GhlHub/open_ethernet_switch/ip_repo/INTERFACES.md

# Digital IP interface contracts

These contracts describe the checked-in RTL and KR260 production integration.
They do not extend port speed support. Manifests select source files, public
module names and catalog versions; changing the public hardware interface
requires a new catalog version and regeneration of dependent block designs.
The processor ABI is versioned separately by the capability register.

## Common packet and reset rules

Every switch-facing packet interface is 16-bit AXI-Stream with two byte
enables. A transfer occurs only with TVALID and TREADY high. The producer
holds data, byte enables, TLAST and any TUSER stable while stalled. TLAST
marks the final word; odd-length frames use one valid byte there. Byte lane
zero carries the earlier byte. Frames exclude the Ethernet preamble and FCS
at this boundary. Receive interfaces with TUSER convey frame error status.
An AXI-Stream slave is an input to the IP, not necessarily network ingress:
a port's slave stream transmits toward its PHY; the fabric's slave streams
receive from those ports.

Reset signals are active low. Integrators must provide domain-appropriate
reset release and stable clocks. Coordinated reset discards in-flight
packets, buffer ownership, learned addresses and hardware counter intervals.
Link-down/flush controls are the normal operational mechanism for removing
a port; arbitrary independent reset of a live producer/consumer is not an
advertised lossless recovery mechanism. The MAC additionally reclocks its
reset release internally. Existing CDC reports still require review; these
contracts are not physical CDC sign-off.

## Package boundaries

| Catalog name | Version / public module | Clocks and reset inputs | Interfaces / ownership |
| --- | --- | --- | --- |
| `gem_port` | 2.0 / `switch_gem_port` | `clk/rst_n`; `gem_rx_clk/gem_rx_rst_n`; `gem_tx_clk/gem_tx_rst_n` | 16-bit packet streams, PS GEM external RX-write/TX-read FIFO signals, two local counter banks |
| `pl_port` | 1.2 / `pl_gmii_mac_top` | `clk/rst_n`; `axis_clk/axis_rst_n`; `gtx_clk`, `clk_en` | Packet streams; 32-bit AXI-Lite MAC registers; 8-bit GMII; local counter bank |
| `sfp_port` | 1.1 / `sfp_port_top` | `clk/rst_n`; `axis_clk/axis_rst_n`; `gtx_clk/gtx_rst_n`; `gth_clk/gth_rst_n` | Packet streams; 32-bit AXI-Lite MAC registers; decoded 16-bit GTH data/control; PCS status; local counter bank |
| `switch_fabric` | 2.1 / `switch_fabric` | `clk/rst_n`; `axis_clk/axis_rst_n` | Five physical packet-stream pairs, CPU stream pair, four DDR AXI masters, shared packet buffers/queues, forwarding table, six counter banks |
| `management` | 2.1 / `switch_management` | `clk/rst_n` (production control clock) | 32-bit AXI-Lite controls, link/forward/learn masks, CPU TX ABI identifier and RX tag, statistics mailbox and 13-bank decoder |

In production, the fabric runs at 125 MHz, control at approximately
142.857 MHz, PL GMII at 125 MHz, and SFP PCS/GTH at 125/62.5 MHz. Packet
streams on all packages use `clk`; MAC AXI-Lite uses `axis_clk`.
The GEM FIFO clocks follow the negotiated link. The bridge is tested at
125/25/2.5 MHz, but KR260 GEM0 is restricted to 1 Gb/s by the current board
integration. GEM1 and both PL copper ports support full-duplex 10/100/1000 Mb/s.
SFP currently supports only 1 Gb/s full duplex. Faster SFP settings stored in
configuration are not implemented hardware capabilities.

PL RGMII, receive rate conversion, physical PHY reset and clock generation
remain board-shell dependencies. MDIO is a separate catalog IP. SFP GTH, clock generation and module sideband
protection also remain board-shell dependencies. Their eventual packaging
must preserve delay groups, reference clocks, reset ordering and pin timing.

## Fabric controls and DDR

Port numbering is GEM0=0, GEM1=1, PL0=2, PL1=3, SFP=4, CPU=5.
Physical ingress is `s00_axis` through `s04_axis`; physical egress is
`m00_axis` through `m04_axis`. `cpu_s_axis` receives CPU-originated frames;
`cpu_m_axis` delivers CPU-destined frames.

`m_axi_ing` writes physical ingress packets; `m_axi_egr` reads packets for
physical egress; `m_axi_cpu` reads/writes CPU packet transfers. Data width is
128 bits and address width 32 bits. Integration must preserve AXI handshakes,
burst responses and the DDR address mapping. The production interconnect
ties omitted cache attributes to zero explicitly. CPU AXI DMA descriptors
are owned by the R5/PS DMA path, not these fabric masters. See
[the memory map](../docs/memory-map.md) for allocation and ownership.

`link_up_i`, `link_flush_tog_i`, `fwd_en_i` and `learn_en_i` are provided
in the control domain; the fabric owns their crossings. Link/forward/learn
disable triggers the existing drain/invalidation behavior. CPU TX carries
[per-frame metadata](../docs/cpu-tx-metadata.md) in a mandatory two-byte stream
header; it has no separate override CDC. CPU RX tags are consumed in the
control domain once per retired RX descriptor.

Parameters `STATS_DDR` and `STATS_DEBUG` each accept 0 or 1 and must match
management and firmware. `AGE_TICK_DIVIDE_COUNT` controls the fabric aging
tick (default 25,000,000 cycles); it is shortened only in simulation fixtures.
The SFP's three `AN_*_CYCLES` timers default to short simulation values;
production explicitly sets all three to 1,250,000. Integrators must not
use the simulation defaults for a board image.

## Statistics mailbox

Management owns independent request selection and result storage for each
bank. Each bank has its own four-bit select, level request/acknowledgment,
stable 32-bit value and four-bit registered Gray activity signal. Source
logic owns clear-on-capture. Its handshake is request high, acknowledgment
high, request low, acknowledgment low. A timed-out processor access leaves
that bank's transaction intact while other banks progress. Software accumulates
intervals in memory; web/SNMP clients read those totals and per-bank freshness.

| Global banks | Management pins | Owner |
| --- | --- | --- |
| 0–1 | `gem0_req/acks/values` | GEM0 RX/TX |
| 2–3 | `gem1_req/acks/values` | GEM1 RX/TX |
| 4 | `pl0_req/acks/values` | PL0 |
| 5 | `pl1_req/acks/values` | PL1 |
| 6 | `sfp_req/acks/values` | SFP |
| 7–12 | `fabric_req/acks/values` | CPU, DDR and debug counters |

Flattened value vectors store the lowest bank in the least-significant
32-bit word. Banks 13–15 acknowledge immediately with zero; unimplemented
slots and disabled counter groups return zero. `STATS_TIMEOUT` defaults to
4095 control cycles. Timeout returns `0xFFFFFFFF` without canceling the
request or permitting a new index. Retry the same read and complete release
before selecting another index. See [statistics](../docs/statistics.md).

## Production address ownership

| Base / aperture | Owner |
| --- | --- |
| `0x80000000` / 64 KiB | PS-to-fabric AXI DMA |
| `0x80010000`, `0x80020000` / 64 KiB each | Board PL0/PL1 MDIO |
| `0x80030000` / 64 KiB | Board SFP I2C |
| `0x80040000`, `0x80080000` / 256 KiB each | PL0/PL1 MAC |
| `0x800C0000` / 256 KiB | SFP MAC |
| `0x80100000` / 64 KiB | Management, including indirect statistics |

Management 1.2 retires the CPU override at 0x4C and adds CPU_TX_ABI at 0x54.
Statistics capability bits, bank numbers and interrupt routing are unchanged.
`check_production_bd.py` checks these production addresses and connections.
Do not infer the deployed address map from the separate validation BD's
automatic address assignment.

## Fabric 1.2 MAC-table dump interfaces

`s_axi_dump` is an AXI-Lite slave clocked by fabric `clk` / `rst_n`.
Production maps it to control M08 at 0x80110000; SmartConnect supplies the
PS-control clock crossing. ABI register 0x00 reports 0x4D445001.

`m_axi_dump` is a write-only 128-bit AXI master on the same fabric clock/reset,
connected to HP0 SmartConnect S03. Its 16-beat, 256-byte INCR bursts have full
byte strobes and ID zero. One burst is outstanding at a time, with AxCACHE
tied to 0000 in production. Admission yields to address requests and
outstanding transactions from all four packet-DMA directions. An offered
AWVALID is retained under backpressure; later packet requests cannot retract
that burst.

MAC RAM port A grants dump reads below learning and aging, with preemption
between entries. Reads form 16-entry chunks; DDR waiting never holds the RAM
port. The 32 KiB destination belongs exclusively to DMA until completion,
including after a software timeout. The scan is live, not atomic.
See the [register, record and cache-ownership contract](../docs/mac-table-dump.md).

## PL PHY management (`pl_phy_mdio` 1.1)

One `switch_pl_phy_mdio` instance owns a separate MDIO bus, its IOBUF,
Clause 22 engine, AXI-Lite registers and DP83867 startup/polling sequencer.
`clk` and active-low `rst_n` use the 142.857 MHz control domain in the KR260.
`s_axi` has 32-bit data and 8-bit register addresses; the board reserves
64 KiB at `0x80010000` (PL0, PHY address 2) and `0x80020000` (PL1, address 3).
The existing register layout and divider defaults are preserved. Version 1.1
adds poll hold at offset `0x18` bit 0 and resolved status at `0x10` bit 10.
See [PL speed control](../docs/pl-ethernet-speeds.md) for ownership and sequencing.

`phy_reset_released_i` samples the board's clock-lock/PS-reset request through
two `ASYNC_REG` stages before starting initialization. It is a level, not a
pulse. The physical U19 reset request remains owned by the board shell.
`phy_link_o`, one-cycle `phy_link_change_o`, `init_done_o` and `init_fail_o`
are synchronous to `clk`. Link bits feed management inside the BD; change
pulses join SFP events in the board shell. `mdio_io` and `mdc_o` reach the
board pins directly. Package-pin/electrical constraints remain in board XDC;
this partition does not complete the outstanding external MDIO timing budget.

`INIT_PHY_ADDR`, `INIT_WAIT_CYCLES` and `INIT_POLL_CYCLES` are configurable.
Production retains the prior two-million-cycle startup wait and
1,430,000-cycle polling interval. Simulation models only the external IOBUF
primitive; the actual controller and sequencer come from the package.

PL MAC 1.1 adds `rx_byte_ce_i`, `tx_byte_ce_i`, and `port_mode_o[2:0]`.
Production sets `EXTERNAL_PACING=1`; the board RGMII shell owns rate conversion.
Legacy native GMII fixtures retain shared `clk_en` through the default parameter.
MAC register `0x41c` controls rate and physical enable; see the PL speed guide.

## Independent statistics mailboxes (ABI 2)

Management 2.0 owns one pending read/result per bank. Each endpoint now exports
four Gray clock-progress bits per bank. GEM 2.0 has independent RX/TX selects
(8 bits total); fabric 2.0 has six independent selects (24 bits). Management
exports separate `<endpoint>_select` buses and accepts corresponding
`<endpoint>_activity` buses. PL 1.2 and SFP 1.1 retain their four-bit select and
add four activity bits. Repackage all changed IP together; these interfaces
are not compatible with the former shared select. Source slots remain stable
through ACK release. A timed-out CPU access does not cancel source ownership.
See [statistics](../docs/statistics.md) for the CSR ABI and clock-progress CDC
contract. The serialized native fixture models successful transaction consumption
on request release; the production CSR uses an explicit take pulse, preserving
results across timeouts.

### STP/RSTP prerequisites (fabric and management 2.1)

No external port widths change. Fabric gates ordinary enqueue destinations by
forwarding state, while explicit directed CPU packets bypass it. CPU dequeue
requests pause at ingress-tag FIFO full. Management adds `STP_ABI` +0x58,
`0x53545002`, for firmware compatibility checking. See [protocol integration](../docs/spanning-tree.md).

## 10G SFP MAC/PCS (`sfp_10g_port` 1.0)

Selected by `KR260_SFP_MODE=10g`; the existing `sfp_port` stays the default.
The 10G core exposes 128-bit packet streams with 16 byte enables in the
125 MHz fabric domain, a compatible RX/TX-enable AXI-Lite window in the
management domain, and independent 64-bit/2-bit data/header interfaces in
the 156.25 MHz TX and recovered RX domains. Legacy `charisk` port names carry
sync headers; they are not 8b/10b controls. `rx_bitslip_o` and
`rx_reset_req_o` drive the external GTH shell. See the full
[clock, register, statistics and qualification contract](../docs/sfp-10g.md).

`switch_fabric` adds `SFP_DATA_WIDTH` (16 by default; select 128 with this IP).
Only `s04_axis` and `m04_axis` widths change; other packet ports and the DDR
ABI remain unchanged. Standalone consumers must apply the included upstream
FIFO timing constraints and constrain all status/control CDC paths; merely
packaging the core does not establish timing closure.

## Dual-rate SFP

`sfp_dual_port` preserves the 128-bit stream and AXI-Lite management interfaces
of `sfp_10g_port`. Additional 125/62.5 MHz clocks serve the 1G PCS. Stable mode
request plus a retry toggle cross to the always-on GTH controller; active mode,
ready and error return through synchronizers. See [the complete contract](../docs/sfp-dual.md).
