GhlHub/open_ethernet_switch/docs/ip-partitioning.md

# IP repository partitioning

## Implemented boundaries

The first structural migration separates forwarding/storage from all five
physical port endpoints. No packet pipeline stage, FIFO depth, clock,
reset sequence, register address, counter index or firmware ABI is changed.

```mermaid
flowchart LR
    PS[PS GEM external FIFOs] <--> GEM[gem_port x2<br/>CDC and port counters]
    RGMII[Board RGMII I/O<br/>elastic buffers] <--> PL[pl_port x2<br/>GMII MAC and counters]
    PHY[PL copper PHYs] <--> MDIO[pl_phy_mdio x2<br/>MDIO, initialization and polling]
    MDIO -. link status .-> MGMT
    GT[Board GTH and clocks<br/>SFP sideband] <--> SFP[sfp_port<br/>1000BASE-X MAC and PCS]
    GEM <-->|16-bit AXI-S| FAB
    PL <-->|16-bit AXI-S| FAB
    SFP <-->|16-bit AXI-S| FAB
    subgraph FAB[switch_fabric]
        IN[Physical ingress datapath]
        BUF[Shared buffer manager]
        OUT[Physical egress datapath]
        CPU[CPU virtual-port engines]
        FWD[MAC lookup, learning and aging]
        IN <--> BUF
        OUT <--> BUF
        CPU <--> BUF
        FWD -. destination masks .-> IN
        FWD -. destination masks .-> CPU
    end
    FAB <-->|Four AXI masters| DDR[Board interconnect and PS DDR]
    CPU <-->|16-bit AXI-S| DMA[AMD AXI DMA and R5]
    MGMT[management<br/>AXI-Lite configuration and snapshot mailbox] -. control and status .-> FAB
    GEM -. snapshots .-> MGMT
    PL -. snapshots .-> MGMT
    SFP -. snapshots .-> MGMT
```

`ip_repo/switch_fabric/hdl/switch_fabric.sv` owns the shared buffer manager,
physical ingress/egress, CPU virtual port and forwarding table. The buffer
manager is a sibling of `ingress_datapath`, rather than a child of ingress.
`rtl/dma/ingress_top.sv` remains a compatibility assembly for existing
ingress subsystem tests and instantiates the same ingress datapath.

`ip_repo/gem_port/hdl/switch_gem_port.sv` combines the existing GEM bridge
with its RX and TX counter banks. `rtl/switch_top.sv` is now a wiring
assembly of the fabric and five endpoints, plus the unchanged statistics
bank decoder. It preserves the existing testbench port list. The production board now
uses `ip_repo/production.tcl` to instantiate the catalog cells directly
in `system.bd`; `kr260_pl_top` contains only the physical shells, clocks,
reset synchronizers and physical status/event logic. The two `pl_phy_mdio`
catalog instances now own MDIO, initialization, polling and PHY reset-release
synchronization.

The other three IP manifests package the existing PL MAC, SFP MAC/PCS and
management modules. `scripts/ip_sources.py` deduplicates shared leaf RTL
and orders packages before modules. Simulation, out-of-context switch
synthesis and the board build use this resolver, replacing the board's
recursive source glob. `build/switch_top_files.f` is a compatibility list;
the manifests are authoritative.

## Interface contracts

| Boundary | Contract |
| --- | --- |
| Physical fabric ingress | `s00_axis` through `s04_axis`; 16-bit data, two byte enables, valid/ready/last, bad-frame `TUSER`; fabric clock |
| Physical fabric egress | `m00_axis` through `m04_axis`; 16-bit data, two byte enables, valid/ready/last; fabric clock |
| CPU streams | Existing 16-bit `cpu_s_axis`/`cpu_m_axis`, fabric clock |
| DDR | Existing 32-bit addresses, 128-bit data, physical write master, physical read master, bidirectional CPU master |
| Port numbering | GEM0=0, GEM1=1, PL0=2, PL1=3, SFP=4, CPU=5 |
| Statistics | Existing four-phase request/ack handshake; select remains stable through completion; held snapshot data and clear-on-read behavior unchanged |
| Counter ownership | GEM banks 0–3 inside GEM endpoints; PL/SFP banks 4–6 inside MAC endpoints; CPU/DDR/debug banks 7–12 inside fabric |
| Resets and CDC | Physical endpoint CDC remains local; fabric runs at 100 MHz; management and MAC control use the existing PS control clock |
| Parameters | Fabric exposes only `STATS_DDR`, `STATS_DEBUG`, and `AGE_TICK_DIVIDE_COUNT`; imported package geometry is not a GUI parameter |

The adapters retain their existing frame/FCS conventions and backpressure
rules. This migration does not add PL 10/100 operation or faster SFP rates.
The CPU override and RX-tag paths retain the baseline behavior, including
the previously documented unresolved concurrency/CDC concerns.

## Verification

The reference is Git commit `6b180e0138d5592cfb80078a9a2517d63013927b`.
`scripts/check_ip_equivalence.py` retrieves its original switch and ingress
assemblies and compares them with the partitioned design under identical
inputs and DDR responses. Every external output is compared after every
relevant clock edge, including statistics data/acknowledgments. It also
runs the existing packet-content and control regression assertions.

All four combinations of `STATS_DDR` and `STATS_DEBUG` passed:

| DDR/debug | Clock samples | Outputs per sample | Completed snapshot reads |
| --- | ---: | ---: | ---: |
| 0/0 | 29,922 | 114 | 1,591 |
| 1/0 | 29,922 | 114 | 1,366 |
| 0/1 | 29,922 | 114 | 1,543 |
| 1/1 | 29,922 | 114 | 1,326 |

The stimulus covers GEM0-to-CPU forwarding, byte contents, link flushing,
blocked data traffic, reserved control-frame delivery, CPU destination
override and return to normal forwarding. Snapshot traffic spans all bank
and slot values, including unmapped banks. This is a finite simulation
comparison, not formal equivalence or an all-port stress proof.

The module regression passed buffer-manager, ingress, egress, GEM bridge,
egress/GEM integration, PL adapters, SFP port, CPU port, forwarding,
statistics, multirate GEM, ingress pipeline and diagnostics tests.

Packaging checks compare staged source contents with the manifests and
assert interface widths, unique clock associations, resets and the legal
fabric parameter list. Generated IP wrappers are additionally exercised
through the same comparison fixture; Vivado integrity checking alone did
not detect its initial erroneous promotion of package constants into
module parameters. The packaging script explicitly corrects this.

Local evidence is under `build/ip_refactor/`. The isolated board project
is `build/vivado_kr260_modular/`; its implementation result is recorded in
[verification](verification.md).

## Production block design

`system.bd` contains `fabric`, `gem0`, `gem1`, `pl0`, `pl1`, `sfp` and
`management` catalog cells alongside PS, DMA and SmartConnect. All ten
physical AXI-Stream connections, CPU streams, three DDR masters, MAC control
interfaces, GEM external FIFOs, interrupts and management controls connect
inside the BD. The existing address windows remain:

| Block | Base | Window |
| --- | --- | --- |
| CPU AXI DMA | `0x80000000` | 64 KiB |
| PL0 / PL1 MDIO | `0x80010000` / `0x80020000` | 64 KiB each |
| SFP I2C | `0x80030000` | 64 KiB |
| PL0 / PL1 MAC | `0x80040000` / `0x80080000` | 256 KiB each |
| SFP MAC | `0x800C0000` | 256 KiB |
| Management | `0x80100000` | 64 KiB |

`STATS_DDR` and `STATS_DEBUG` now configure both fabric and management IP
parameters in the build Tcl. Physical instances stay under `u_pl`, preserving
the RGMII delay groups and forwarded-clock constraint targets.
The clock-crossing XDC is processed late, after vendor and board clocks
exist; its numeric bounds are unchanged.
`axi_attributes.tcl` explicitly retains the previous `AxCACHE=0000` ties
on all four switch DDR channels; Vivado otherwise defaults omitted cache
attributes to `0011`. There is no firmware ABI change. A missing or stale
catalog fails the build before BD creation; regenerate it into a fresh
directory and set `KR260_IP_CATALOG`.

To compare the generated production datapath with the original assembly:

```sh
python3 scripts/check_ip_equivalence.py \
  --production-bd build/ip_refactor/production_bd/project/kr260_switch.gen/sources_1/bd/system \
  --catalog build/ip_catalog
```

This fixture uses the generated instance connections and packaged source
snapshots, checks the stream/control wiring against the prior native
assembly, and reuses the packet/counter equivalence stimulus. Only aging
and PCS timers are accelerated in fixture-local wrapper copies. PS/DDR
interconnect and physical I/O remain simulation boundaries. The all-counter
production assembly passed this comparison and completed bitstream generation
with routed WNS +0.018 ns and hold slack +0.011 ns; see
[build results and limitations](verification.md#2026-09-25-production-catalog-block-design).
It was downloaded over JTAG and passed settled GEM1/PL0 connectivity, SNMP
and HTTP checks; see the board acceptance results in verification.md.

## Independent package verification

Each digital IP now owns a test manifest. `make -C sim sim-ip-regression`
runs its focused tests from native and packaged RTL, then the existing
whole-switch comparisons for all four counter configurations. Public tops
are independently elaborated; GEM/PL/SFP and management have direct boundary
benches, while fabric behavior is checked through its constituent suites
and assembly miter. See [suite coverage and commands](../ip_repo/README.md#independent-ip-regression-suites).

## PL PHY-management extraction

`pl_phy_mdio` 1.0 moves both MDIO controllers and their two-stage PHY-reset
release synchronizers into the catalog. The production instances are `mdio0`
and `mdio1`; each owns initialization, polling and its bidirectional IOBUF.
The former 34 AXI-Lite signals between `system.bd` and `kr260_pl_top` are now
internal BD interfaces. The board retains PHY reset requests, RGMII I/O and
clock generation. PHY link status connects directly to management; change
pulses join existing SFP events in the physical shell.

No firmware registers, PHY addresses, polling intervals or startup delays
change. This split makes PHY management independently reusable before the
more constraint-sensitive RGMII migration. Its focused tests use actual
packaged RTL with a simulation-only IOBUF primitive. They cover Clause 22
read/write framing, status clear, startup at both board PHY addresses,
strap/ID failure, link polling, disconnect/reconnect, PHY reset and deferred
CPU requests during polling. Existing MDIO arbitration/AXI race investigations
remain listed in the inventory; packaging does not resolve those issues.

## Remaining migration and acceptance work

The reusable **digital** IP boundaries are implemented. The complete
physical-port/block-design migration proposed for the final architecture
is not complete:

1. Move each RGMII I/O/elastic-buffer shell inside its copper-port IP,
   composing it with the now-packaged `pl_phy_mdio` management block,
   with scoped constraints and explicit per-instance IDELAY groups. The
   current board constraints name `u_pl/u_rgmii0` and `u_pl/u_rgmii1`, so
   this requires a separate physical timing check.
2. Move the GTH, PCS clock generator and SFP sideband shell into the SFP
   package, with reproducible vendor-IP dependencies and scoped clocks.
3. Management 1.1 now includes the statistics decoder. The separate
   `partition_validation.bd` remains an interface test fixture; keep its
   clock/address defaults distinct from production.
4. Add a six-port concurrent packet scoreboard with randomized DDR
   backpressure/errors, exhaustion, link/reset transitions and ownership
   invariants. Existing subsystem tests and the finite comparison do not
   replace that coverage.
5. After routed timing/CDC review, repeat board DHCP, ping, forwarding,
   GEM1 speed, SNMP/web and SD configuration regression. Do not attribute
   existing STP or transient outage problems to this structural migration
   without new evidence.

The partitioned all-counter image has subsequently been loaded over JTAG.
DHCP, CPU connectivity, web/SNMP access and settled endpoint forwarding
passed on the connected GEM1/PL0 path. Initial DHCP/endpoint losses were
observed before recovery; see [hardware results](verification.md). The
remaining all-port and speed-matrix acceptance work still applies.

## Management 1.1 and reproducible acceptance

The statistics router is now inside `switch_management`; production no longer
uses a router module reference. Public per-bank signals replace the four raw
mailbox wires. Firmware ABI, register offsets and bank numbering are unchanged.
A public-wrapper test covers all 256 index values, clear-on-read isolation,
invalid banks, saturation, backpressure and stopped-clock timeout recovery.

[Interface contracts](../ip_repo/INTERFACES.md) describe the current packages.
`python3 scripts/verify_ip_flow.py` regenerates a catalog and production BD in
fresh output directories, then runs package and assembly regressions. Use
`--implement` to add PNR/bitstream generation and routed reports. The production
packet miter substitutes the CSR source with its existing mailbox stimulus;
the separate management-wrapper test verifies AXI-Lite-to-bank behavior.

## Fabric 1.2: MAC-table dump master

The dump engine belongs inside `switch_fabric`, alongside MAC port-A arbitration
and packet-DMA admission tracking. It exports `m_axi_dump` (128-bit writes, HP0
S03) and `s_axi_dump` (control M08, 0x80110000), both on the fabric clock.
Control SmartConnect now has nine outputs and HP0 SmartConnect four inputs.
Manifest-owned source/tests and native/production equivalence include both new
interfaces. Physical shells and the HP1 CPU stream DMA retain their interfaces.
See [the complete contract](mac-table-dump.md).
