GhlHub/open_ethernet_switch/docs/source-notices.md

# Source provenance and reference material

[`rtl/pl_gmii/open_eth_mac_1g_switch.sv`](../rtl/pl_gmii/open_eth_mac_1g_switch.sv)
identifies its origin as `open_eth_mac_1g` from
[GhlHub/open-ethernet-cores](https://github.com/GhlHub/open-ethernet-cores).
Its existing `GPL-3.0-or-later` SPDX identifier and modification notice (now four changes, the newest a descriptor-ring "full" width bug fix) are
preserved. The notice describes the module rename, permanently enabled
destination acceptance for switch operation, and two clock-domain-crossing changes
(the reset inputs are reclocked into each clock domain, and the data read
pointers are published one word per clock), with no change to the frame path. The original import does not
record an upstream commit ID.

[`rtl/mdio/open_eth_mdio_master.sv`](../rtl/mdio/open_eth_mdio_master.sv) is
identified by its header as imported from the same upstream project's
`open_eth_sgmii_pcs_pma` IP (a Clause 22 MDIO station-management master,
upstream only instantiated inside that larger core, used standalone here).
Its existing `GPL-3.0-or-later` SPDX identifier is preserved; the original
import does not record an upstream commit ID.
[`rtl/mdio/mdio_controller.sv`](../rtl/mdio/mdio_controller.sv) (and its sim
model) is new project code wrapping it with an AXI4-Lite register interface.

A copy of the GPL version 3 text is included at
[`LICENSES/GPL-3.0-or-later.txt`](../LICENSES/GPL-3.0-or-later.txt).
This inventory does not assign a new license to the other source files.

[`rtl/sfp_pcs/autoneg_1000base_x.sv`](../rtl/sfp_pcs/autoneg_1000base_x.sv)
records design cross-checks against
[freecores/1000base-x](https://github.com/freecores/1000base-x), specifically
`rtl/verilog/ge_1000baseX_tx.v` and `ge_1000baseX_an.v`. No reference commit is recorded. These are design references, not protocol
conformance evidence. The implementation's reductions and unverified areas are
listed in its header and the [development inventory](inventory.md).

The GEM adapters refer to the AMD
[Zynq UltraScale+ technical reference manual (UG1085)](https://docs.amd.com/r/en-US/ug1085-zynq-ultrascale-trm).
The local downloaded PDF is reference material and is not included in the
source commit. Board documentation is available in the
[KR260 user guide (UG1092)](https://docs.amd.com/r/en-US/ug1092-kr260-starter-kit).

The SFP transceiver wrapper depends on AMD Transceiver Wizard IP. Its
[`gth_sfp_ip.xci`](../rtl/sfp_pcs/ip/gth_sfp_ip.xci) configuration is included;
generated vendor implementation and simulation output products are not.
Regenerating them requires the appropriate Vivado installation and vendor
terms. The portable GTH loopback model is separate from that vendor IP.

The PL Ethernet clock wrapper similarly depends on AMD Clocking Wizard IP,
configured by [`pl_eth_clk_gen_ip.xci`](../rtl/pl_gmii/ip/pl_eth_clk_gen_ip.xci).
The RGMII hardware adapter uses AMD UltraScale+ I/O, delay and clock primitives.
`mdio_controller.sv` uses an AMD IOBUF for the bidirectional pin. Its comments
report prior isolated synthesis checks; this inventory tested the portable
wrapper rather than the vendor primitive. Portable models do not replace the
hardware dependencies.

The local XTP743 carrier schematic package is retained as reference material
and excluded from Git, including its PDF, ZIP and vendor readme. The readme
identifies the material as proprietary and does not itself grant redistribution
rights. [Board integration notes](board-integration.md) record the exact
schematic revision/hash, source download, and the facts used by this design.

## FreeRTOS-LTS dependency

[`third_party/FreeRTOS-LTS`](../third_party/FreeRTOS-LTS) is a Git submodule of
[FreeRTOS/FreeRTOS-LTS](https://github.com/FreeRTOS/FreeRTOS-LTS), tracking
`202604-LTS` and pinned to `0b25dc50bae4cb971c7a459b109e52ab2f01a6b8`.
Upstream component licenses/notices remain in that checkout; no vendor sources
are copied into the project RTL. See [dependency setup](../third_party/README.md)
for initialization. The reference does not provide a KR260 BSP, application,
network driver or boot image.

The R5 linker script in `software/r5/linker.ld` is adapted from AMD
embeddedsw 2026.1 `scripts/linker_files/lscript_r5.ld.in` and retains its MIT
copyright/SPDX header. The application links the generated AMD standalone BSP;
its source notices remain in the installed/generated BSP.

## R5 storage and authentication dependencies

The vendored [libpayload USB subset](../third_party/libpayload_usb/README.md)
comes from coreboot revision `7a5f91cae93cc0a5420bb3569f521a8addb228ed`.
Its BSD-3-Clause notices remain in the source files; the import README
describes the R5 adaptation and mass-storage compatibility changes.

[FatFs R0.15](../third_party/fatfs/README.md) supplies FAT filesystem access;
its upstream notice remains in `ff.c` and `ff.h`. The local configuration
does not enable formatting or exFAT.

The [SHA-256 implementation](../third_party/sha256/README.md) retains Brad
Conte's public-domain attribution and records its import through AMD
embeddedsw 2026.1 and the local unsigned-shift correction. It is used by
the administrator password verifier.

IP packaging copies project RTL and its existing notices into generated
catalogs. The new `ip_repo` boundaries do not change source licensing;
generated catalogs and vendor output products are excluded from Git.

## 10G Ethernet dependency

The [verilog-ethernet subset](../third_party/verilog-ethernet/README.md) is
MIT-licensed and pinned to `77320a9471d19c7dd383914bc049e02d9f4f1ffb`.
Its COPYING file and individual source notices remain intact; the import
manifest records per-file SHA-256 hashes. Upstream RTL is unmodified.
The local 10G wrapper, fault handling and board integration are separate.
