GhlHub/open_ethernet_switch/tb/tb_ingress_top.sv

// tb_ingress_top.sv
//
// Self-checking smoke test for the ingress DMA path (5x ingress_port_wr +
// ingress_dma_wr + buf_mgr_core), backed by a behavioral AXI4 memory
// model standing in for PS DDR:
//   1. send a short frame into port 0, destined to port 2 -> confirm
//      buf_mgr_core's port-2 queue gets the right {bufid, length}, and
//      the AXI memory actually contains the right bytes at the buffer's
//      DDR address
//   2. send a frame with tuser (CRC error) asserted at tlast -> confirm
//      it's dropped: no destination ever sees it, buffer freed straight
//      back (checked indirectly: alloc still succeeds afterwards)
//   3. send two frames concurrently on two different ports -> confirm
//      the shared AXI write engine's arbitration serves both correctly
//      with no data corruption/mixing between them

`timescale 1ns/1ps

module tb_ingress_top;
  import buf_mgr_pkg::*;
  import axi_dma_pkg::*;

  logic clk = 0;
  logic rst_n = 0;

  logic [NUM_PHYS_PORTS-1:0][15:0] s_axis_tdata;
  logic [NUM_PHYS_PORTS-1:0][1:0]  s_axis_tkeep;
  logic [NUM_PHYS_PORTS-1:0]      s_axis_tvalid;
  logic [NUM_PHYS_PORTS-1:0]      s_axis_tlast;
  logic [NUM_PHYS_PORTS-1:0]      s_axis_tuser;
  logic [NUM_PHYS_PORTS-1:0]      s_axis_tready;

  logic [NUM_PHYS_PORTS-1:0][NUM_PORTS-1:0] dest_mask_i;
  logic [NUM_PHYS_PORTS-1:0]                 dest_mask_valid_i;

  logic [AXI_ID_W-1:0]   m_axi_awid;
  logic [AXI_ADDR_W-1:0] m_axi_awaddr;
  logic [7:0]            m_axi_awlen;
  logic [2:0]             m_axi_awsize;
  logic [1:0]             m_axi_awburst;
  logic                   m_axi_awvalid;
  logic                   m_axi_awready;
  logic [AXI_DATA_W-1:0]  m_axi_wdata;
  logic [AXI_STRB_W-1:0]  m_axi_wstrb;
  logic                   m_axi_wlast;
  logic                   m_axi_wvalid;
  logic                   m_axi_wready;
  logic [AXI_ID_W-1:0]    m_axi_bid;
  logic [1:0]             m_axi_bresp;
  logic                   m_axi_bvalid;
  logic                   m_axi_bready;

  logic [NUM_PORTS-1:0]               dequeue_req;
  logic [NUM_PORTS-1:0]               dequeue_valid;
  logic [NUM_PORTS-1:0][BUF_ID_W-1:0] dequeue_bufid;
  logic [NUM_PORTS-1:0][LENGTH_W-1:0] dequeue_length;
  logic [NUM_PORTS-1:0]               release_req;
  logic [NUM_PORTS-1:0][BUF_ID_W-1:0] release_bufid;
  logic [NUM_PORTS-1:0]               release_gnt;

  logic                cpu_alloc_req = 1'b0;
  logic                cpu_alloc_gnt;
  logic [BUF_ID_W-1:0] cpu_alloc_bufid;
  logic                     cpu_enqueue_req = 1'b0;
  logic [BUF_ID_W-1:0]      cpu_enqueue_bufid = '0;
  logic [LENGTH_W-1:0]      cpu_enqueue_length = '0;
  logic [NUM_PORTS-1:0]     cpu_enqueue_destmask = '0;
  logic                     cpu_enqueue_gnt;

  ingress_top dut (
    .clk                       (clk),
    .rst_n                     (rst_n),
    .s_axis_tdata              (s_axis_tdata),
    .s_axis_tkeep              (s_axis_tkeep),
    .s_axis_tvalid             (s_axis_tvalid),
    .s_axis_tlast              (s_axis_tlast),
    .s_axis_tuser              (s_axis_tuser),
    .s_axis_tready             (s_axis_tready),
    .dest_mask_i               (dest_mask_i),
    .dest_mask_valid_i         (dest_mask_valid_i),
    .m_axi_awid                (m_axi_awid),
    .m_axi_awaddr              (m_axi_awaddr),
    .m_axi_awlen               (m_axi_awlen),
    .m_axi_awsize              (m_axi_awsize),
    .m_axi_awburst             (m_axi_awburst),
    .m_axi_awvalid             (m_axi_awvalid),
    .m_axi_awready             (m_axi_awready),
    .m_axi_wdata               (m_axi_wdata),
    .m_axi_wstrb               (m_axi_wstrb),
    .m_axi_wlast               (m_axi_wlast),
    .m_axi_wvalid               (m_axi_wvalid),
    .m_axi_wready               (m_axi_wready),
    .m_axi_bid                  (m_axi_bid),
    .m_axi_bresp                (m_axi_bresp),
    .m_axi_bvalid                (m_axi_bvalid),
    .m_axi_bready                (m_axi_bready),
    .dequeue_req_i_passthru      (dequeue_req),
    .dequeue_valid_o_passthru    (dequeue_valid),
    .dequeue_bufid_o_passthru    (dequeue_bufid),
    .dequeue_length_o_passthru   (dequeue_length),
    .release_req_i_passthru      (release_req),
    .release_bufid_i_passthru    (release_bufid),
    .release_gnt_o_passthru      (release_gnt),
    .cpu_alloc_req_i              (cpu_alloc_req),
    .cpu_alloc_gnt_o              (cpu_alloc_gnt),
    .cpu_alloc_bufid_o            (cpu_alloc_bufid),
    .cpu_enqueue_req_i            (cpu_enqueue_req),
    .cpu_enqueue_bufid_i          (cpu_enqueue_bufid),
    .cpu_enqueue_length_i         (cpu_enqueue_length),
    .cpu_enqueue_destmask_i       (cpu_enqueue_destmask),
    .cpu_enqueue_gnt_o            (cpu_enqueue_gnt),
    .link_up_i ({NUM_PORTS{1'b1}}),
    .flush_req_i ('0),
    .flush_busy_o ()
  );

  // Covers 16 buffers' worth of DDR (bufid 0-15). Confirmed by bisection:
  // Icarus Verilog 12.0's elaboration pass scales terribly with this
  // module's unpacked `mem` array once it crosses ~64KB (fine/instant at
  // 32KB, hangs for minutes-plus at 128KB and up) -- independent of
  // BASE_ADDR. The buf_mgr_core free list is a FIFO filled 0..NUM_BUFFERS-1
  // at boot, so this smoke test's handful of allocations always land on
  // low bufids; 16 buffers is generous headroom for it.
  axi_mem_bfm #(.MEM_BYTES(16 * BUFFER_BYTES), .BASE_ADDR(DDR_BASE_ADDR)) u_mem (
    .clk           (clk),
    .rst_n         (rst_n),
    .s_axi_awid    (m_axi_awid),
    .s_axi_awaddr  (m_axi_awaddr),
    .s_axi_awlen   (m_axi_awlen),
    .s_axi_awsize  (m_axi_awsize),
    .s_axi_awburst (m_axi_awburst),
    .s_axi_awvalid (m_axi_awvalid),
    .s_axi_awready (m_axi_awready),
    .s_axi_wdata   (m_axi_wdata),
    .s_axi_wstrb   (m_axi_wstrb),
    .s_axi_wlast   (m_axi_wlast),
    .s_axi_wvalid  (m_axi_wvalid),
    .s_axi_wready  (m_axi_wready),
    .s_axi_bid     (m_axi_bid),
    .s_axi_bresp   (m_axi_bresp),
    .s_axi_bvalid  (m_axi_bvalid),
    .s_axi_bready  (m_axi_bready),
    .s_axi_arid    ('0),
    .s_axi_araddr  ('0),
    .s_axi_arlen   ('0),
    .s_axi_arsize  ('0),
    .s_axi_arburst ('0),
    .s_axi_arvalid (1'b0),
    .s_axi_arready (),
    .s_axi_rid     (),
    .s_axi_rdata   (),
    .s_axi_rresp   (),
    .s_axi_rlast   (),
    .s_axi_rvalid  (),
    .s_axi_rready  (1'b0)
  );

  always #4 clk = ~clk;

  int errors = 0;

  task automatic wait_cycles(input int n);
    repeat (n) @(posedge clk);
  endtask

  // send one frame's bytes into physical port `port`, packed two at a
  // time into 16-bit words (tkeep=2'b01 on a trailing single byte, i.e.
  // an odd-length frame); `data` holds the payload, `bad` asserts tuser
  // (CRC error) on the last transfer.
  task automatic send_frame(input int port, input byte data[], input bit bad);
    int n;
    int i;
    logic [15:0] word;
    logic [1:0]  keep;
    bit          is_last;
    n = data.size();
    i = 0;
    while (i < n) begin
      if (i + 1 < n) begin
        word    = {data[i+1], data[i]};
        keep    = 2'b11;
        is_last = (i + 2 >= n);
      end else begin
        word    = {8'h00, data[i]};
        keep    = 2'b01;
        is_last = 1'b1;
      end
      s_axis_tdata[port]  = word;
      s_axis_tkeep[port]  = keep;
      s_axis_tvalid[port] = 1'b1;
      s_axis_tlast[port]  = is_last;
      s_axis_tuser[port]  = is_last ? bad : 1'b0;
      // wait for tready
      @(posedge clk);
      while (!s_axis_tready[port]) @(posedge clk);
      i = i + ((keep == 2'b11) ? 2 : 1);
    end
    s_axis_tvalid[port] = 1'b0;
    s_axis_tlast[port]  = 1'b0;
    s_axis_tuser[port]  = 1'b0;
  endtask

  task automatic do_dequeue(input int port, output logic [BUF_ID_W-1:0] bufid, output logic [LENGTH_W-1:0] length);
    int timeout;
    bit timed_out;
    dequeue_req[port] = 1'b1;
    timeout = 0;
    timed_out = 1'b0;
    while (!dequeue_valid[port] && !timed_out) begin
      @(posedge clk);
      timeout++;
      if (timeout > 5000) begin
        $display("FAIL: dequeue on port %0d timed out", port);
        errors++;
        timed_out = 1'b1;
      end
    end
    if (timed_out) begin
      bufid = 'x; length = 'x;
    end else begin
      bufid  = dequeue_bufid[port];
      length = dequeue_length[port];
    end
    dequeue_req[port] = 1'b0;
    @(posedge clk);
  endtask

  task automatic do_release(input int port, input logic [BUF_ID_W-1:0] bufid);
    int timeout;
    bit timed_out;
    release_req[port]   = 1'b1;
    release_bufid[port] = bufid;
    timeout = 0;
    timed_out = 1'b0;
    while (!release_gnt[port] && !timed_out) begin
      @(posedge clk);
      timeout++;
      if (timeout > 5000) begin
        $display("FAIL: release on port %0d timed out", port);
        errors++;
        timed_out = 1'b1;
      end
    end
    release_req[port] = 1'b0;
    @(posedge clk);
  endtask

  task automatic confirm_no_dequeue(input int port, input int cycles);
    dequeue_req[port] = 1'b1;
    for (int c = 0; c < cycles; c++) begin
      @(posedge clk);
      if (dequeue_valid[port]) begin
        $display("FAIL: unexpected dequeue on port %0d", port);
        errors++;
      end
    end
    dequeue_req[port] = 1'b0;
  endtask

  logic [BUF_ID_W-1:0] bufid_a;
  logic [LENGTH_W-1:0] length_a;

  initial begin
    s_axis_tdata  = '0;
    s_axis_tkeep  = '0;
    s_axis_tvalid = '0;
    s_axis_tlast  = '0;
    s_axis_tuser  = '0;
    dest_mask_i        = '0;
    dest_mask_valid_i  = '0;
    dequeue_req   = '0;
    release_req   = '0;
    release_bufid = '0;

    repeat (5) @(posedge clk);
    rst_n = 1'b1;
    wait_cycles(NUM_BUFFERS + 20); // buf_mgr_core's free-list fill sweep

    // ---- 1: short frame, port 0 -> port 2 (odd length, exercises the
    // trailing tkeep=2'b01 single-byte word) ----
    dest_mask_i[0]       = NUM_PORTS'(1) << 2;
    dest_mask_valid_i[0] = 1'b1;
    begin
      byte data[];
      data = new[21];
      for (int i = 0; i < 21; i++) data[i] = byte'(i + 8'h10);
      send_frame(0, data, 1'b0);
    end

    do_dequeue(2, bufid_a, length_a);
    if (length_a !== LENGTH_W'(21)) begin
      $display("FAIL: frame1 length=%0d, expected 21", length_a);
      errors++;
    end else begin
      $display("PASS: frame1 enqueued to port 2, bufid=%0d length=%0d", bufid_a, length_a);
    end

    begin
      logic ok = 1'b1;
      int base = int'(bufid_a) * BUFFER_BYTES; // u_mem.mem is rebased by BASE_ADDR(DDR_BASE_ADDR)
      for (int i = 0; i < 21; i++) begin
        if (u_mem.mem[base + i] !== 8'(i + 8'h10)) begin
          $display("FAIL: DDR byte %0d = %02h, expected %02h", i, u_mem.mem[base+i], 8'(i+8'h10));
          ok = 1'b0;
          errors++;
        end
      end
      if (ok) $display("PASS: DDR content matches the transmitted frame (odd length)");
    end
    do_release(2, bufid_a);

    // ---- 2: bad frame (CRC error) -- must never reach any destination ----
    dest_mask_i[0]       = NUM_PORTS'(1) << 3;
    dest_mask_valid_i[0] = 1'b1;
    begin
      byte data[];
      data = new[10];
      for (int i = 0; i < 10; i++) data[i] = byte'(i);
      send_frame(0, data, 1'b1); // tuser=1 on tlast -> dropped
    end
    fork
      confirm_no_dequeue(0, 30);
      confirm_no_dequeue(1, 30);
      confirm_no_dequeue(2, 30);
      confirm_no_dequeue(3, 30);
      confirm_no_dequeue(4, 30);
      confirm_no_dequeue(5, 30);
    join
    $display("PASS: bad frame dropped, no destination ever saw it");

    // ---- 3: two frames concurrently on two different ports ----
    dest_mask_i[1]       = NUM_PORTS'(1) << 4;
    dest_mask_valid_i[1] = 1'b1;
    dest_mask_i[3]       = NUM_PORTS'(1) << 4;
    dest_mask_valid_i[3] = 1'b1;
    fork
      begin
        byte data[];
        data = new[16];
        for (int i = 0; i < 16; i++) data[i] = byte'(8'hA0 + i);
        send_frame(1, data, 1'b0);
      end
      begin
        byte data[];
        data = new[24];
        for (int i = 0; i < 24; i++) data[i] = byte'(8'hB0 + i);
        send_frame(3, data, 1'b0);
      end
    join

    begin
      logic [BUF_ID_W-1:0] b1, b2;
      logic [LENGTH_W-1:0] l1, l2;
      int base1, base2;
      bit ok = 1'b1;
      do_dequeue(4, b1, l1);
      do_dequeue(4, b2, l2);
      // one of these should be the 16B frame, the other the 24B frame
      if (!((l1 == LENGTH_W'(16) && l2 == LENGTH_W'(24)) || (l1 == LENGTH_W'(24) && l2 == LENGTH_W'(16)))) begin
        $display("FAIL: concurrent frames lengths = %0d, %0d, expected {16,24}", l1, l2);
        errors++;
        ok = 1'b0;
      end
      if (ok) begin
        base1 = int'(b1) * BUFFER_BYTES;
        base2 = int'(b2) * BUFFER_BYTES;
        if (l1 == LENGTH_W'(16)) begin
          for (int i = 0; i < 16; i++) if (u_mem.mem[base1+i] !== 8'(8'hA0+i)) begin errors++; ok = 1'b0; end
          for (int i = 0; i < 24; i++) if (u_mem.mem[base2+i] !== 8'(8'hB0+i)) begin errors++; ok = 1'b0; end
        end else begin
          for (int i = 0; i < 24; i++) if (u_mem.mem[base1+i] !== 8'(8'hB0+i)) begin errors++; ok = 1'b0; end
          for (int i = 0; i < 16; i++) if (u_mem.mem[base2+i] !== 8'(8'hA0+i)) begin errors++; ok = 1'b0; end
        end
        if (ok) $display("PASS: two concurrent frames both DMA'd correctly, no data mixed between them");
        else     $display("FAIL: concurrent frame DDR content mismatch");
      end
      do_release(4, b1);
      do_release(4, b2);
    end

    if (errors == 0) $display("=== ALL TESTS PASSED ===");
    else              $display("=== %0d TEST(S) FAILED ===", errors);

    $finish;
  end

  initial begin
    #5_000_000;
    $display("FAIL: global testbench timeout");
    $finish;
  end

endmodule
