GhlHub/open_ethernet_switch/rtl/mac_table/mac_addr_resolver.sv

// mac_addr_resolver.sv
//
// One instance per switch port (5 physical + CPU); the module that was
// missing between the MAC address table (rtl/mac_table/mac_addr_table_top.sv)
// and the ingress datapath's dest_mask_i/dest_mask_valid_i inputs (see
// ingress_port_wr.sv/cpu_port_top.sv's own headers -- both call this out
// as "placeholder until the MAC table is wired in").
//
// Snoops this port's own ingress AXI4-Stream (the same s_axis_* wires
// driving ingress_port_wr -- this module only *reads* them, it never
// drives s_axis_tready) to extract the first 12 bytes of every frame:
// destination MAC (bytes 0-5) then source MAC (bytes 6-11). Once both are
// captured, issues one lookup request (destination MAC -> forwarding
// decision) and one learn request (source MAC -> "this MAC lives behind
// this port") to this port's own dedicated learn/lookup ports on the
// shared mac_addr_table_top instance.
//
// dest_mask_o/dest_mask_valid_o feed ingress_port_wr's dest_mask_i/
// dest_mask_valid_i directly:
//   - lookup hit  -> dest_mask_o = the table's learned one-hot-or-wider
//     port mask for that destination, excluding this ingress port and
//     truncated to NUM_PORTS bits. A same-port-only hit resolves to zero
//     (drop), never a flood. The table supports PORTMASK_W=8 ports; we use 6.
//   - lookup miss -> flood: every port except this one's own. This is
//     also the correct behavior for broadcast/multicast destinations
//     without any separate detection logic, since a multicast bit set in
//     a destination MAC can never match a learned (always-unicast-source)
//     table entry -- it always misses, and always floods.
//   - a malformed/short frame (tlast before 12 bytes captured) resolves
//     straight to dest_mask_o=0 (queue_mgr.sv's enqueue path treats an
//     all-zero destmask as a drop, no refcount taken) instead of issuing
//     any lookup at all -- ingress_port_wr's S_ENQ_WAIT has no timeout,
//     so leaving dest_mask_valid_o low forever on a runt frame would wedge
//     this port permanently.
//
// Reserved link-layer control frames (destination MAC 01:80:C2:00:00:0x,
// the IEEE 802.1D "Bridge Group Address" block: STP/RSTP/MSTP BPDUs at
// ...:00, the Slow Protocols multicast shared by LACP/OAM at ...:02, LLDP's
// nearest-bridge address at ...:0E, and the rest of that 16-address block) --
// a MAC bridge must never relay these out any port, only ever consume them
// locally, in EVERY port state including one with forwarding disabled (a
// blocked STP port must still receive and answer BPDUs). is_ctrl_dest below
// intercepts the lookup result for exactly these 16 addresses and forces the
// destination to the CPU port alone, unconditionally: not flooded, not
// gated by fwd_en_i (unlike ordinary traffic -- see below), and never
// resolved from the table (a reserved address is never a valid learned
// unicast destination anyway, so the lookup always misses regardless). The
// source MAC is still learned normally (subject to learn_en_i, same as any
// other frame) -- a control frame's source is a real host address like any
// other. One compare covers every protocol in the block: which byte of the
// received frame identifies which protocol is a question for whatever
// consumes it after the CPU port (not decoded here), so this same trap
// already covers STP today and needs no RTL change to also carry LLDP,
// LACP or any other protocol in the reserved block later.
//
// learn_en_i/fwd_en_i (from the CPU's per-port control state, see
// rtl/board/rx_diag_regs.sv's FWD_SET/CLR and LEARN_SET/CLR registers, both
// default-enabled so a design with no software driving them behaves exactly
// as before this feature existed): learn_en_i gates learn_req_o outright;
// fwd_en_i gates dest_mask_o for ORDINARY (non-control) frames only --
// forwarding disabled on this port means nothing this port receives is
// relayed anywhere (dest_mask_o forced to 0), matching 802.1D's Blocking/
// Listening/Discarding port states. switch_top.sv synchronizes these
// software-controlled levels into the fabric clock domain.
//
// dest_mask_valid_o is held (not pulsed) from when a result lands until
// the *next* frame's first byte is accepted, which cannot happen before
// ingress_port_wr has consumed the current one (dest_mask_valid_i gates
// its own enqueue, and it won't return to S_RECV -- able to accept a new
// frame's byte 0 -- until after that): the two are naturally sequenced by
// construction, so no busy_i/backpressure handling is needed here beyond
// that.
//
// Internal state (word_pos_q/dest_mac_q/src_mac_q/mask_ready_q/
// dest_mask_q) is updated via combinationally-computed "_next" signals,
// each with exactly one NBA per register in the always_ff -- see
// ingress_port_wr.sv's header for the confirmed Icarus Verilog hazard
// (12.0 and 13.0 alike) this pattern avoids: a register read
// combinationally by build a downstream consumer (here, learn_mac_o/
// lookup_mac_o) on the same cycle it's also updated can otherwise observe
// the wrong (post-edge) value.

module mac_addr_resolver
  import buf_mgr_pkg::*;
  import mac_table_pkg::*;
#(
  parameter int PORT_ID = 0,
  parameter int DATA_WIDTH = 16
) (
  input  logic clk,
  input  logic rst_n,

  // snooped ingress AXI4-Stream (same wires feeding ingress_port_wr's
  // s_axis_*; not driven here). s_axis_tkeep_i is intentionally unused:
  // any frame that ends (for any reason, at any byte count) before this
  // module has captured all 12 destination+source MAC bytes is treated
  // uniformly as malformed/short via word_pos_q + tlast alone (see the
  // "malformed/short frame" handling below) -- there is no case where the
  // exact tkeep value on a partial final word changes that outcome.
  input  logic [DATA_WIDTH-1:0] s_axis_tdata_i,
  input  logic [DATA_WIDTH/8-1:0] s_axis_tkeep_i,
  input  logic         s_axis_tvalid_i,
  input  logic         s_axis_tlast_i,
  input  logic         s_axis_tready_i,

  // per-port control state (see header); both default-tied enabled by
  // switch_top.sv until software drives them
  input  logic learn_en_i,
  input  logic fwd_en_i,

  // -> ingress_port_wr's dest_mask_i/dest_mask_valid_i
  output logic [NUM_PORTS-1:0] dest_mask_o,
  output logic                 dest_mask_valid_o,

  // held for exactly as long as dest_mask_valid_o/dest_mask_o (same
  // register lifetime, see their own comments below) whenever this frame
  // matched the reserved control block -- informational only (future
  // per-port control-frame counters/hooks), nothing here consumes it
  output logic ctrl_frame_o,

  // -> mac_learn_port #(.PORT_ID(PORT_ID))
  output logic             learn_req_o,
  output logic [MAC_W-1:0] learn_mac_o,

  // -> mac_lookup_port #(.PORT_ID(PORT_ID))
  output logic              lookup_req_o,
  output logic [MAC_W-1:0]  lookup_mac_o,
  input  logic               lookup_result_valid_i,
  input  logic               lookup_result_hit_i,
  input  logic [PORTMASK_W-1:0] lookup_result_port_mask_i
);

  // every port except this one's own -- see header note on flood/miss/
  // broadcast handling
  localparam logic [NUM_PORTS-1:0] FLOOD_MASK = ~(NUM_PORTS'(1) << PORT_ID);

  // CPU is always buf_mgr_pkg::NUM_PORTS' last slot (see switch_top.sv's
  // port numbering table); masked by FLOOD_MASK so the CPU's own resolver
  // instance (PORT_ID == CPU_PORT_ID) correctly resolves a reserved-address
  // frame it might itself originate to 0 (drop), not to itself.
  localparam int CPU_PORT_ID = NUM_PORTS - 1;
  localparam logic [NUM_PORTS-1:0] CPU_MASK =
    (NUM_PORTS'(1) << CPU_PORT_ID) & FLOOD_MASK;

  // IEEE 802.1D reserved "Bridge Group Address" block, 01:80:C2:00:00:00
  // through :0F -- see header. dest_mac's byte order here is the same
  // human-readable order the rest of this module already uses (bit 47 =
  // first transmitted byte); the low nibble (any of the 16 addresses) is
  // don't-care.
  localparam logic [43:0] CTRL_BLOCK_PREFIX = 44'h0180_C200_000;

  logic [2:0]  word_pos_q; // 0..5, next word to capture; 6 = parked,
                            // waiting for this frame's own tlast
  logic [47:0] dest_mac_q, src_mac_q;
  logic                 mask_ready_q;
  logic [NUM_PORTS-1:0] dest_mask_q;

  // declared after dest_mac_q (Icarus Verilog 13.0 requires a signal's
  // declaration to textually precede a procedural reference to it in the
  // same module -- see this project's other files for the same note)
  wire is_ctrl_dest = (dest_mac_q[47:4] == CTRL_BLOCK_PREFIX);

  wire word_accept = s_axis_tvalid_i && s_axis_tready_i;

  logic [2:0]  word_pos_next;
  logic [47:0] dest_mac_next, src_mac_next;
  logic                 mask_ready_next;
  logic [NUM_PORTS-1:0] dest_mask_next;
  logic                 ctrl_frame_q, ctrl_frame_next;
  logic                 issue_req;

  always_comb begin
    word_pos_next   = word_pos_q;
    dest_mac_next   = dest_mac_q;
    src_mac_next    = src_mac_q;
    mask_ready_next = mask_ready_q;
    dest_mask_next  = dest_mask_q;
    ctrl_frame_next = ctrl_frame_q;
    issue_req       = 1'b0;

    if (word_accept) begin
      // first byte of a new frame: whatever resolved for the previous one
      // no longer applies to this one
      if (word_pos_q == 3'd0) mask_ready_next = 1'b0;

      if (DATA_WIDTH == 128) begin
        if (word_pos_q == 0) begin
          for (integer b=0;b<6;b=b+1) begin
            dest_mac_next[47-8*b -: 8] = s_axis_tdata_i[8*b +: 8];
            src_mac_next[47-8*b -: 8] = s_axis_tdata_i[48+8*b +: 8];
          end
          issue_req = (&s_axis_tkeep_i[11:0]);
          if (!issue_req) begin
            mask_ready_next=1; dest_mask_next=0; ctrl_frame_next=0;
          end
        end
        word_pos_next = s_axis_tlast_i ? 0 : 6;
      end else begin
      if (word_pos_q < 3'd6) begin
        // case on a constant lane index, not a variable/register-indexed
        // part-select write -- see rtl/dma/ingress_port_wr.sv's own
        // accumulator for the same rationale (confirmed Icarus bug with
        // the latter).
        // each 16-bit word holds {byte i+1, byte i} (tdata[7:0]=earlier
        // byte, tdata[15:8]=later byte -- the same convention as every
        // other word-to-byte accumulator in this project); swapped back
        // here so dest_mac_next/src_mac_next hold the MAC in its normal,
        // human-readable byte order (dest_mac[47:40] = the first
        // transmitted byte), matching what a real MAC address means, not
        // just an internally-self-consistent opaque 48-bit key
        unique case (word_pos_q)
          3'd0:    dest_mac_next[47:32] = {s_axis_tdata_i[7:0], s_axis_tdata_i[15:8]};
          3'd1:    dest_mac_next[31:16] = {s_axis_tdata_i[7:0], s_axis_tdata_i[15:8]};
          3'd2:    dest_mac_next[15:0]  = {s_axis_tdata_i[7:0], s_axis_tdata_i[15:8]};
          3'd3:    src_mac_next[47:32]  = {s_axis_tdata_i[7:0], s_axis_tdata_i[15:8]};
          3'd4:    src_mac_next[31:16]  = {s_axis_tdata_i[7:0], s_axis_tdata_i[15:8]};
          default: src_mac_next[15:0]   = {s_axis_tdata_i[7:0], s_axis_tdata_i[15:8]}; // word_pos_q==5
        endcase
        if (word_pos_q == 3'd5) issue_req = 1'b1; // source MAC now complete
      end

      if (s_axis_tlast_i) begin
        word_pos_next = '0; // reset for the next frame regardless
        if (word_pos_q < 3'd5) begin
          // malformed/short frame: never captured both MACs (word_pos_q
          // parks at 6 once it does -- see its declaration comment -- so
          // this must check "never reached 5", not "isn't currently 5":
          // that parked state is the *normal* case for any frame longer
          // than 12 bytes, not a malformed one), no lookup was issued --
          // resolve straight to "drop" (see header note)
          mask_ready_next = 1'b1;
          dest_mask_next  = '0;
          ctrl_frame_next = 1'b0;
        end
      end else if (word_pos_q < 3'd6) begin
        word_pos_next = word_pos_q + 1'b1;
      end
      end
    end

    if (lookup_result_valid_i) begin
      mask_ready_next = 1'b1;
      ctrl_frame_next = is_ctrl_dest;
      if (is_ctrl_dest)
        // reserved control block: always to the CPU alone, never flooded,
        // never gated by fwd_en_i -- see the header note on why a blocked
        // port must still deliver these
        dest_mask_next = CPU_MASK;
      else
        dest_mask_next = fwd_en_i
          ? (lookup_result_hit_i
              ? (lookup_result_port_mask_i[NUM_PORTS-1:0] & FLOOD_MASK)
              : FLOOD_MASK)
          : '0; // forwarding disabled on this port: nothing it receives is relayed
    end
  end

  always_ff @(posedge clk or negedge rst_n) begin
    if (!rst_n) begin
      word_pos_q   <= '0;
      dest_mac_q   <= '0;
      src_mac_q    <= '0;
      mask_ready_q <= 1'b0;
      dest_mask_q  <= '0;
      ctrl_frame_q <= 1'b0;
    end else begin
      word_pos_q   <= word_pos_next;
      dest_mac_q   <= dest_mac_next;
      src_mac_q    <= src_mac_next;
      mask_ready_q <= mask_ready_next;
      dest_mask_q  <= dest_mask_next;
      ctrl_frame_q <= ctrl_frame_next;
    end
  end

  assign dest_mask_valid_o = mask_ready_q;
  assign dest_mask_o       = dest_mask_q;
  assign ctrl_frame_o      = ctrl_frame_q;

  // learn_mac_o/lookup_mac_o drive from the *_next combinational signals,
  // not dest_mac_q/src_mac_q: issue_req and the MAC's own final 16 bits
  // are both decided this same cycle (word_pos_q==5's word_accept), so
  // the register itself is still one cycle stale here -- mac_learn_port/
  // mac_lookup_port latch mac_i the same edge req_o is asserted, so this
  // needs to be combinationally current, not the pre-edge register.
  assign learn_req_o  = issue_req && learn_en_i;
  assign learn_mac_o  = src_mac_next;
  assign lookup_req_o  = issue_req;
  assign lookup_mac_o  = dest_mac_next;

endmodule
